Stenkelfled/ws2811/V1.0/include/ledbuffer.h

 /*
 * ledbuffer.h
 *
 * Created: 28.03.2014 10:48:58
 *  Author: stenkelfled
 */ 


#ifndef LEDBUFFER_H_
#define LEDBUFFER_H_

#include <compiler.h>
#include <rgbhsv.h>

/*typedef enum{
    normal = 0,
    shift,
    rainbow
}led_mode_t;*/

typedef struct _led_color_t_ led_color_t;

struct _led_color_t_{
    rgbcolor_t color;
    led_color_t *next_led;
}__attribute__((packed));

typedef struct{
    //led_mode_t mode;
    led_color_t* start_led;
	uint16_t remaining_time;
	uint8_t remaining_repititions;
	uint16_t next_sequence;
}__attribute__((packed)) led_group_t;

void color2data(uint8_t* *data, uint8_t color);
void fill_buffer(void);

uint8_t* ledbuffer_get_data_pointer(void);

//void define_group(uint8_t group_id, uint8_t start_led);
void clear_group(uint8_t group_id);
uint8_t append_row_to_group(uint8_t group_id, uint8_t start_led,uint8_t end_led, uint8_t step);
void append_led_to_group(uint8_t group_id, uint8_t led_id);
void color_group(uint8_t group_id, rgbcolor_t color);
void color_led(uint8_t led_id, rgbcolor_t color);

void group_set_properties(uint8_t group_id, uint16_t next_sequence, uint8_t remaining_repititions, uint16_t remaining_time);


#endif /* LEDBUFFER_H_ */
