Stenkelfled/ws2811/V1.0/include/ee_interpreter.h

/*
 * ee_interpreter.h
 *
 * Created: 30.10.2014 17:12:04
 *  Author: stenkelfled
 *
 * interpretes the data from eeprom
 */ 


#ifndef EE_INTERPRETER_H_
#define EE_INTERPRETER_H_

void interprete_eeprom(void);



#endif /* EE_INTERPRETER_H_ */
