Stenkelfled/ws2811/V1.0/include/usb.h

/*
 * usb.h
 *
 * Created: 28.06.2014 14:02:19
 *  Author: stenkelfled
 */ 


#ifndef USB_H_
#define USB_H_

#include <asf.h>

typedef enum{
	msg_none,
	msg_run,
	msg_test
} msg_type_t;

typedef enum{
	test_color_none,
	test_color_red,
	test_color_green,
	test_color_blue,
} test_color_t;

#define EEPROM_NEED_DATA_LENGTH_HIGH	(1<<15)
#define EEPROM_NEED_DATA_LENGTH_LOW		(1<<14)

void usb_start(void);
void usb_power_monitor_init(void);

void usb_rx_ready(void);

//////////////////////////////////////////////////////////////////////////
//usb-driver callbacks
void user_callback_vbus_action(bool b_vbus_high); //voltage on usb-power-line changed
bool my_callback_cdc_enable(void); //host opens device
void my_callback_cdc_disable(void); //host closes device

#endif /* USB_H_ */
