Stenkelfled/ws2811/V1.0/include/seq_processor.h

/*
 * seq_processor.h
 *
 * Created: 09.07.2014 17:43:37
 *  Author: stenkelfled
 */ 


#ifndef SEQ_PROCESSOR_H_
#define SEQ_PROCESSOR_H_

#include <config.h>

typedef struct{
	
} seq_task_t;

#endif /* SEQ_PROCESSOR_H_ */
